xattribution/petal-dish/docs/feed-review/1200-0.25-1.png

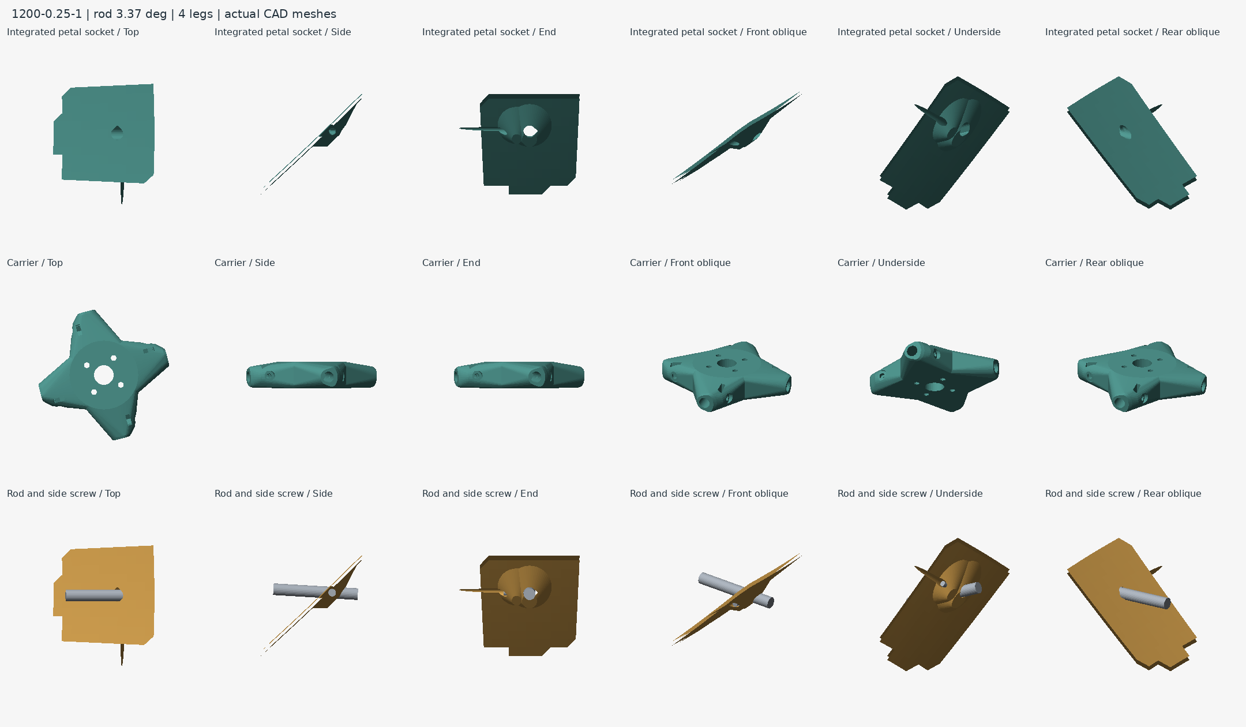
docs/feed-review/1200-0.25-1.png
