xattribution/petal-dish/cad/STL/seam-lever-M3/keeper.stl

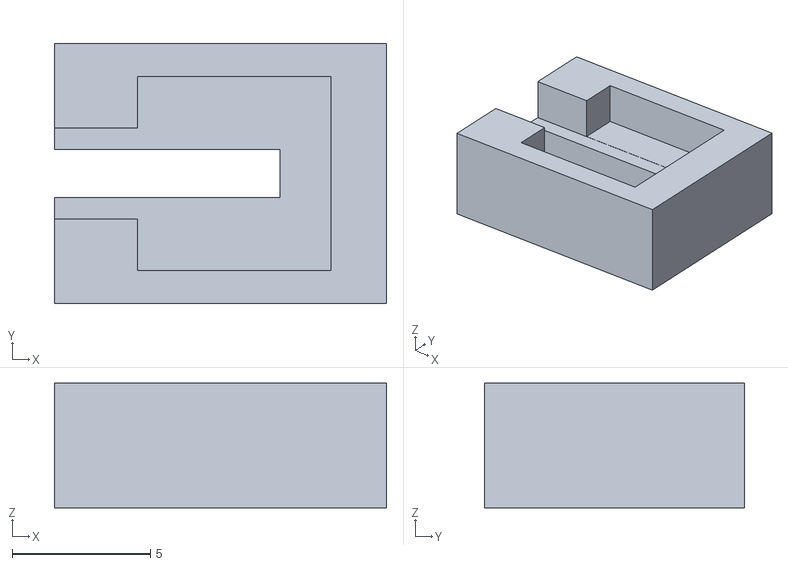
[picture p35: CAD file, 2026-10-02]
cad/STL/seam-lever-M3/keeper.stl
12.0 x 9.40 x 4.50
