xattribution/petal-dish/cad/STL/seam-lever-M4/spring.stl

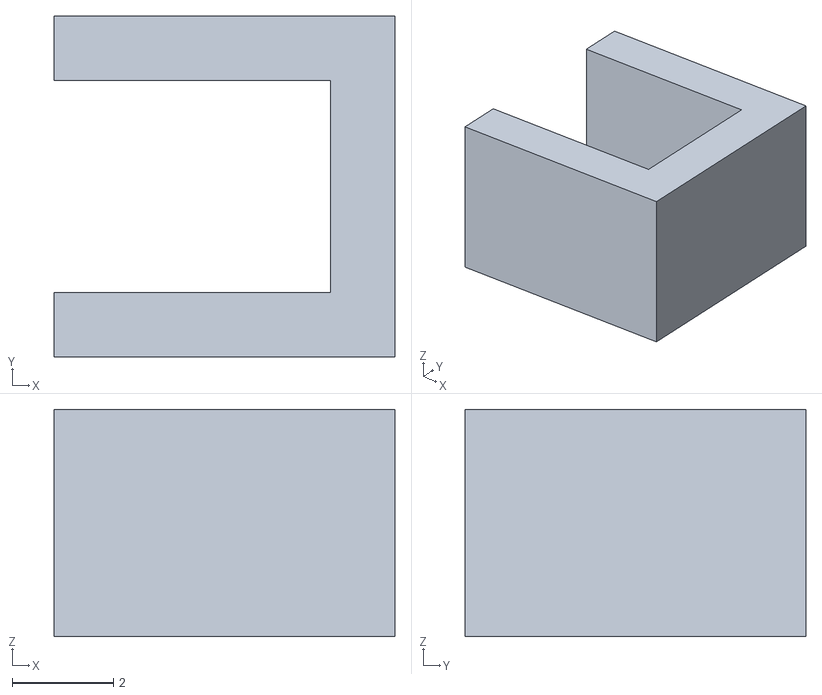
[picture p36: CAD file, 2026-10-02]
cad/STL/seam-lever-M4/spring.stl
6.75 x 6.75 x 4.50
