xattribution/petal-dish/cad/STL/simple-base.stl

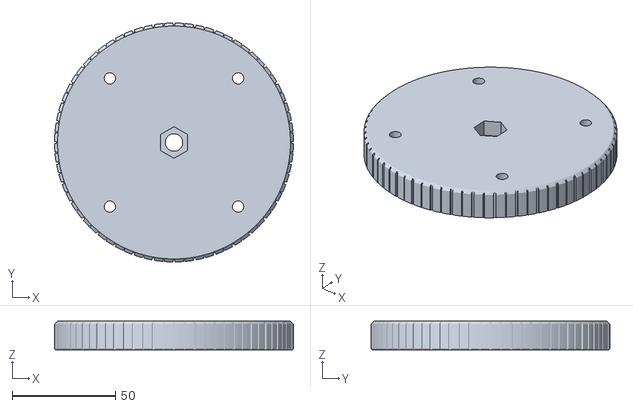
[picture p37: CAD file, 2026-10-08]
cad/STL/simple-base.stl
116.0 x 116.0 x 14.0
