xattribution/petal-dish/cad/STL/simple-yoke-stand.stl

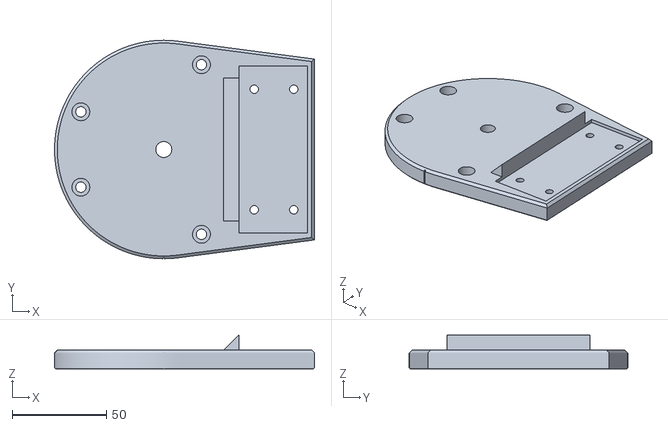
[picture p38: CAD file, 2026-10-08]
cad/STL/simple-yoke-stand.stl
138.0 x 116.0 x 18.0
