xattribution/petal-dish/cad/STL/blank/simple-yoke.stl

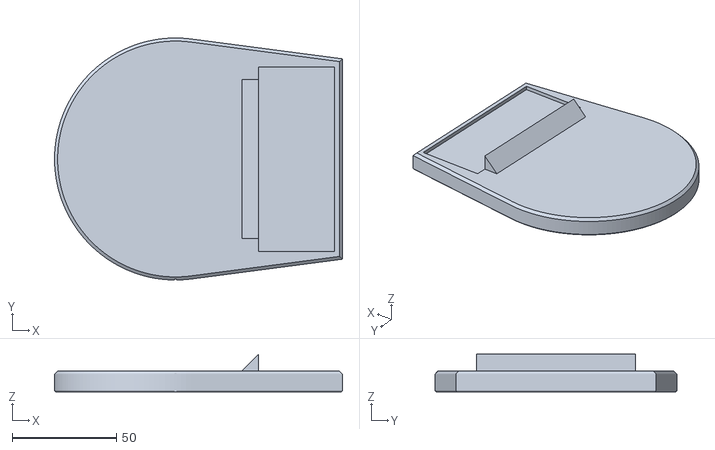
[picture p39: CAD file, 2026-10-06]
cad/STL/blank/simple-yoke.stl
138.0 x 116.0 x 18.0
