xattribution/petal-dish/cad/STL/blank/simple-base.stl

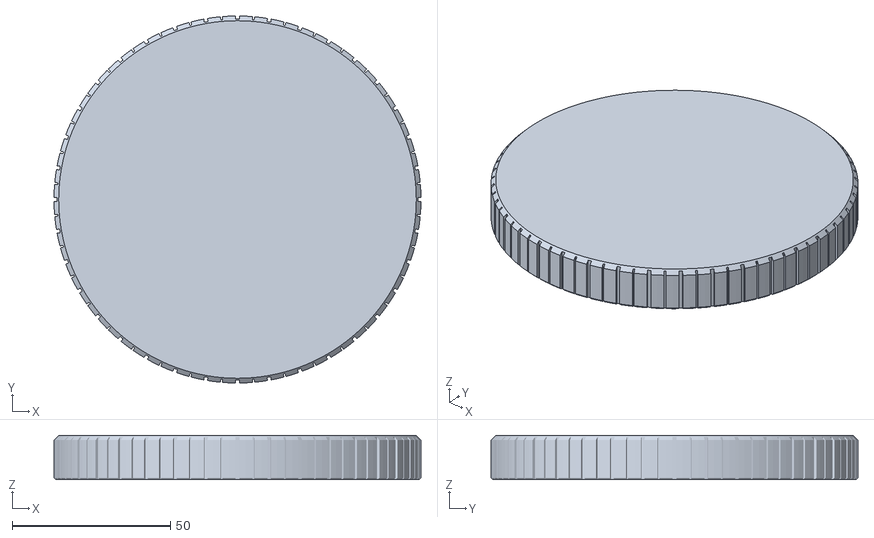
[picture p40: CAD file, 2026-10-06]
cad/STL/blank/simple-base.stl
116.0 x 116.0 x 14.0
