xattribution/petal-dish/cad/STL/blank/simple-upright.stl

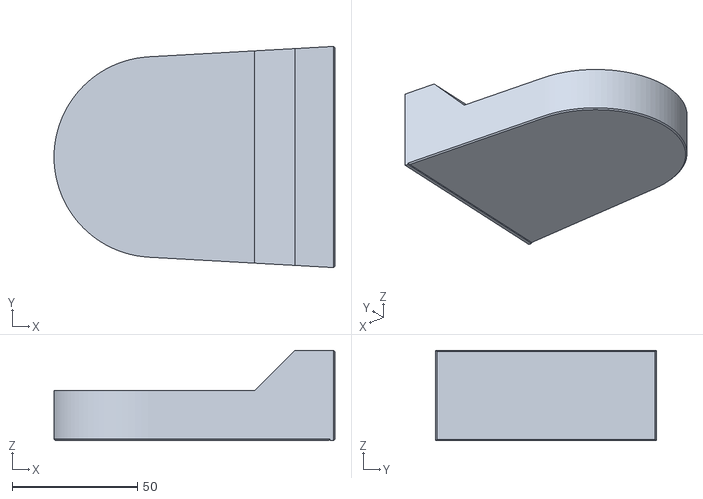
[picture p41: CAD file, 2026-10-06]
cad/STL/blank/simple-upright.stl
112.0 x 88.0 x 36.0
