xattribution/petal-dish/cad/STL/simple-cheek-arc.stl

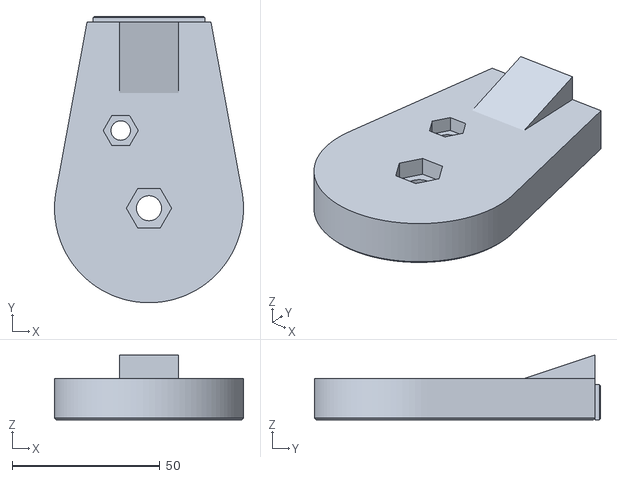
[picture p42: CAD file, 2026-10-04]
cad/STL/simple-cheek-arc.stl
64.0 x 97.0 x 22.0
