xattribution/petal-dish/cad/STL/simple-upright-arc.stl

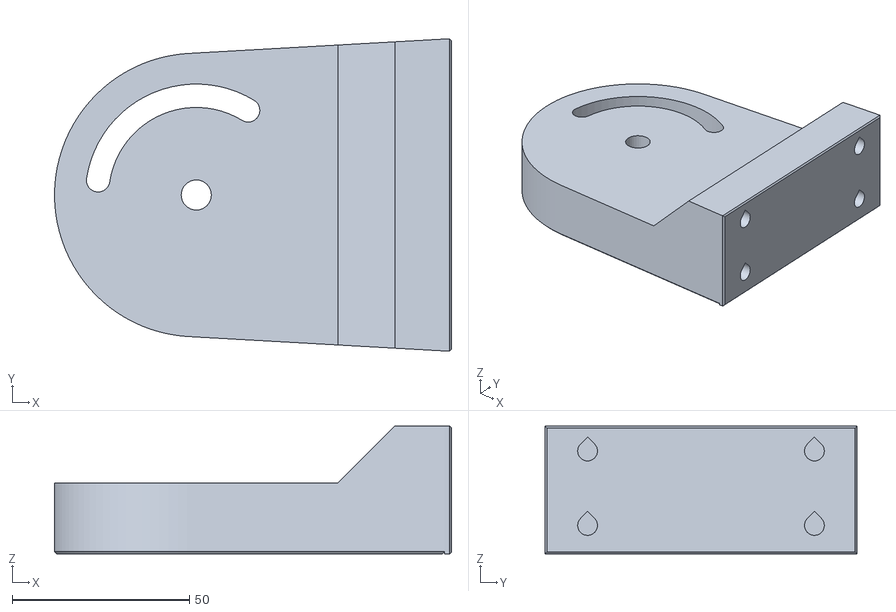
[picture p43: CAD file, 2026-10-02]
cad/STL/simple-upright-arc.stl
112.0 x 88.0 x 36.0
